CharlesVanDen/Woordklok/img/Browserscherm Woordklok.png

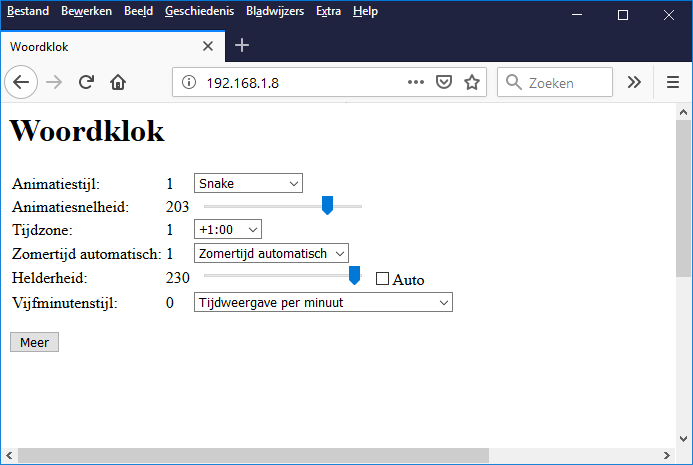
img/Browserscherm Woordklok.png
