CharlesVanDen/Woordklok/img/prg_esp_in_circuit.jpg

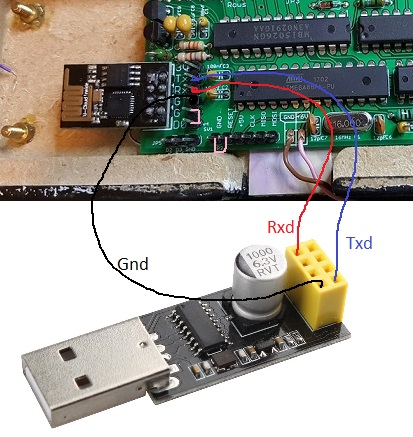
img/prg_esp_in_circuit.jpg
