CharlesVanDen/Woordklok/img/Schema.png

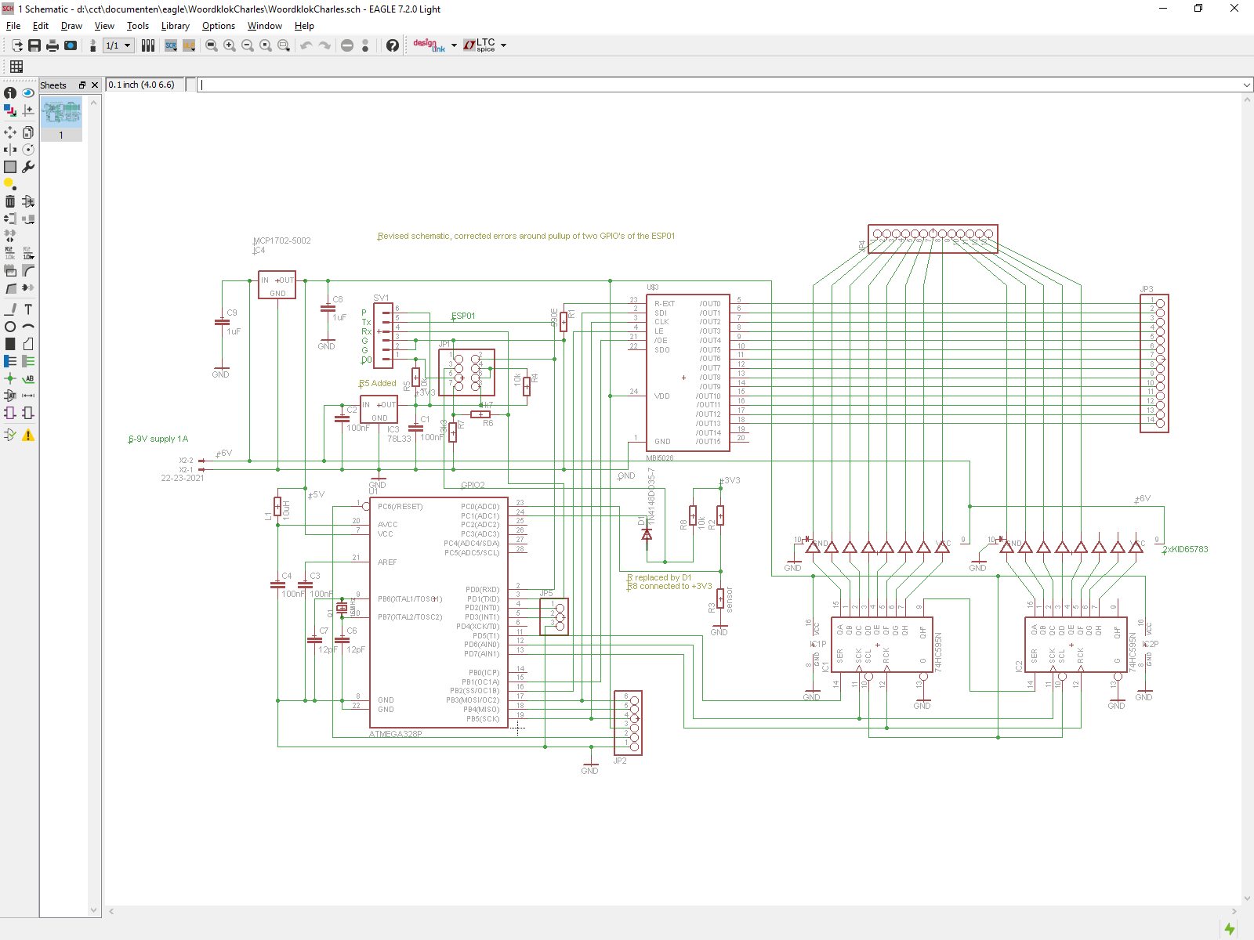
img/Schema.png
