CharlesVanDen/Woordklok/img/ziggomodem.png

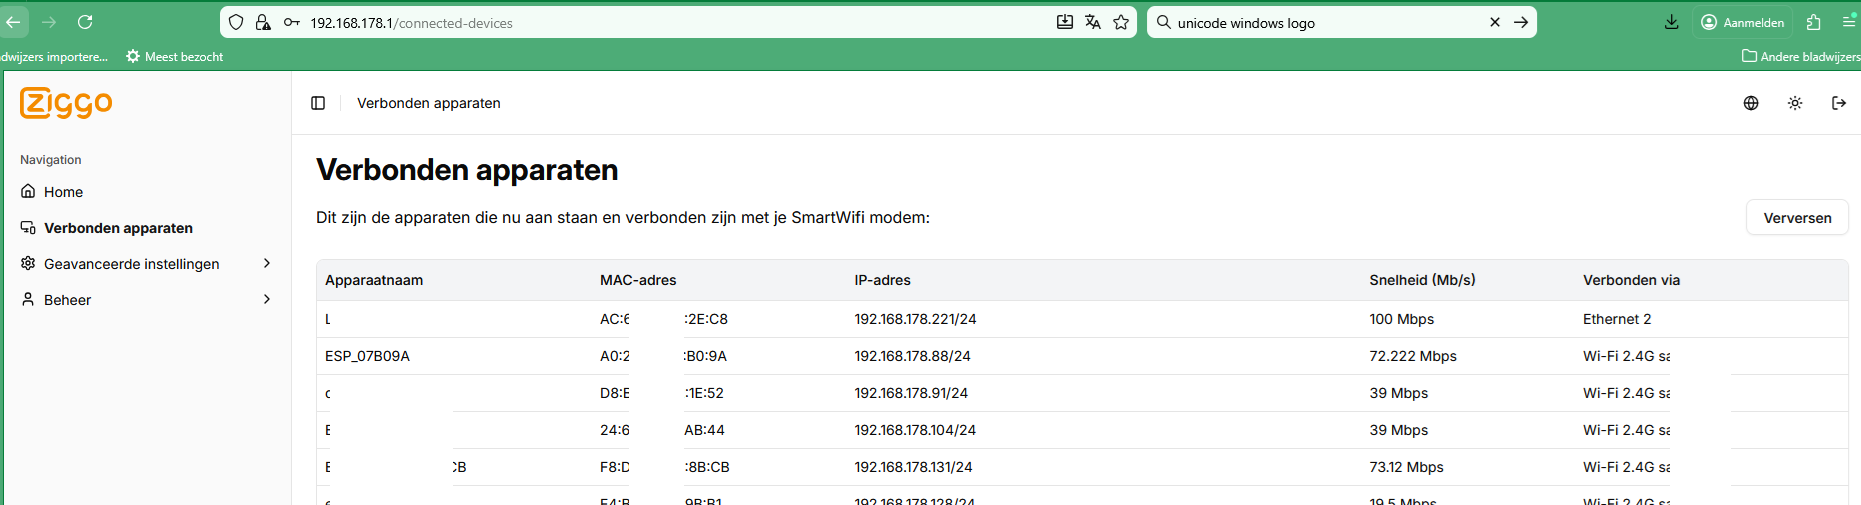
img/ziggomodem.png
